stanley-fork/CorneV4ProMicroEdition/Cases/OLED Covers/No Display Cover Right.stp

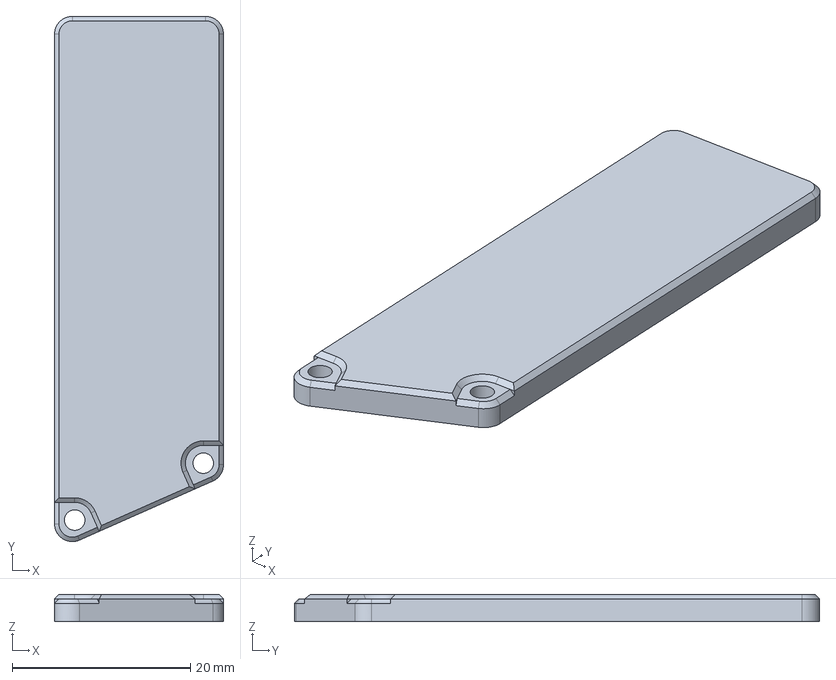
[picture p13: CAD file, 2025-02-19]
Cases/OLED Covers/No Display Cover Right.stp
19.0 x 59.0 x 3.05 mm
